zlosynth/achordion/eurorack/src/system/cv.rs

use core::marker::PhantomData;

use nb::block;

use crate::system::hal::adc::{Adc, Enabled};
use crate::system::hal::hal::adc::Channel;
use crate::system::hal::pac::{ADC1, ADC2};

use achordion_lib::probe::{ProbeDetector, PROBE_SEQUENCE};

const PROBE_SEQUENCE_LEN: usize = PROBE_SEQUENCE.len();

pub struct Cv<A, P> {
    pin: P,
    probe_detector: ProbeDetector<'static, PROBE_SEQUENCE_LEN>,
    value: f32,
    input_range: (f32, f32),
    was_plugged: bool,
    was_unplugged: bool,
    _adc: PhantomData<A>,
}

macro_rules! cv {
    ($adc:ident) => {
        impl<P: Channel<$adc, ID = u8>> Cv<$adc, P> {
            pub fn new(pin: P, input_range: (f32, f32)) -> Self {
                Self {
                    pin,
                    probe_detector: ProbeDetector::new(&PROBE_SEQUENCE),
                    value: 0.0,
                    input_range,
                    was_plugged: false,
                    was_unplugged: false,
                    _adc: PhantomData,
                }
            }

            // NOTE: Prevent inlining to avoid duplicating ADC HAL code for each CV input.
            // This method is called 10 times (5 CVs × 2 ADCs), and inlining would
            // duplicate ~2KB of register configuration code per call site (~4KB total).
            #[inline(never)]
            pub fn start_sampling(&mut self, adc: &mut Adc<$adc, Enabled>) {
                adc.start_conversion(&mut self.pin);
            }

            // NOTE: Prevent inlining to avoid duplicating ADC HAL code for each CV input.
            // This method is called 10 times (5 CVs × 2 ADCs), and inlining would
            // duplicate ~2KB of register configuration code per call site (~4KB total).
            #[inline(never)]
            pub fn finish_sampling(&mut self, adc: &mut Adc<$adc, Enabled>) {
                let was_connected = self.connected();

                let sample: u32 = block!(adc.read_sample()).unwrap();
                self.value = transpose_adc(sample as f32, adc.slope());
                self.probe_detector
                    .write(is_high(sample, adc.slope(), self.input_range));

                let is_connected = self.connected();
                self.was_plugged = !was_connected && is_connected;
                self.was_unplugged = was_connected && !is_connected;
            }

            pub fn connected(&mut self) -> bool {
                !self.probe_detector.detected()
            }

            pub fn value(&self) -> f32 {
                self.value
            }

            pub fn was_plugged(&self) -> bool {
                self.was_plugged
            }

            pub fn was_unplugged(&self) -> bool {
                self.was_unplugged
            }
        }
    };
}

cv!(ADC1);
cv!(ADC2);

fn transpose_adc(sample: f32, slope: u32) -> f32 {
    (slope as f32 - sample) / slope as f32
}

fn is_high(sample: u32, slope: u32, input_range: (f32, f32)) -> bool {
    // Calculate what does center of probe voltage translates to the range of
    // the input.
    let max_probe = 3.3;
    let center = (input_range.0 - max_probe / 2.0) / (input_range.0 - input_range.1);
    transpose_adc(sample as f32, slope) > center
}
